joshbrew/Digital-Spectroscope/demo_app/src/assets/chickenbreast.png

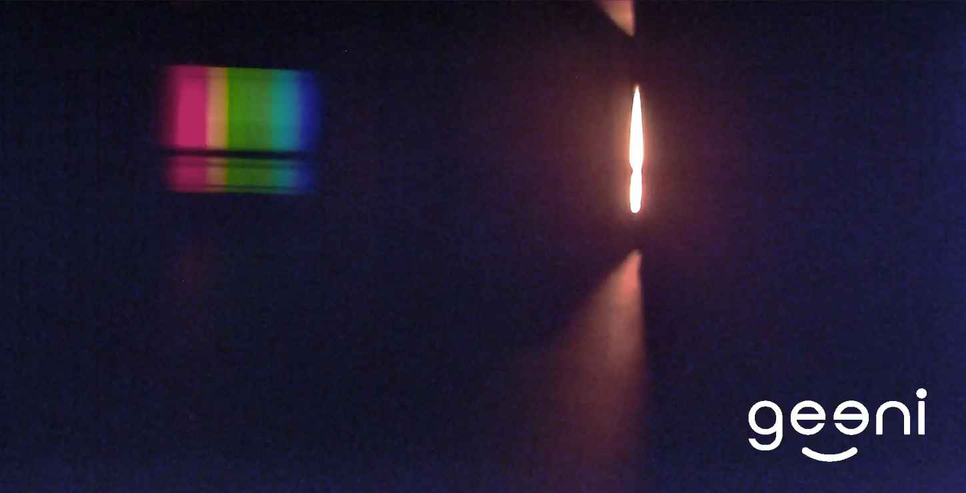
demo_app/src/assets/chickenbreast.png
