joshbrew/Digital-Spectroscope/demo_app/src/assets/chickenfat.png

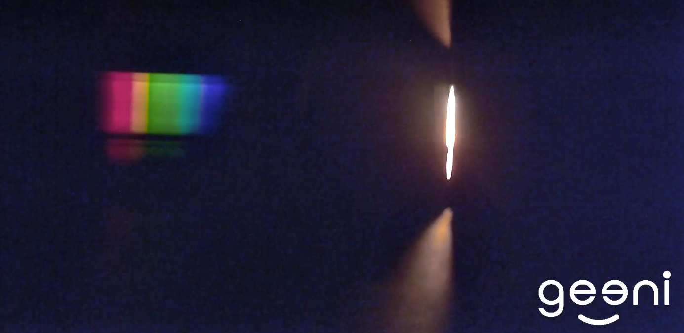
demo_app/src/assets/chickenfat.png
