joshbrew/Digital-Spectroscope/demo_app/src/assets/shrimp.jpg

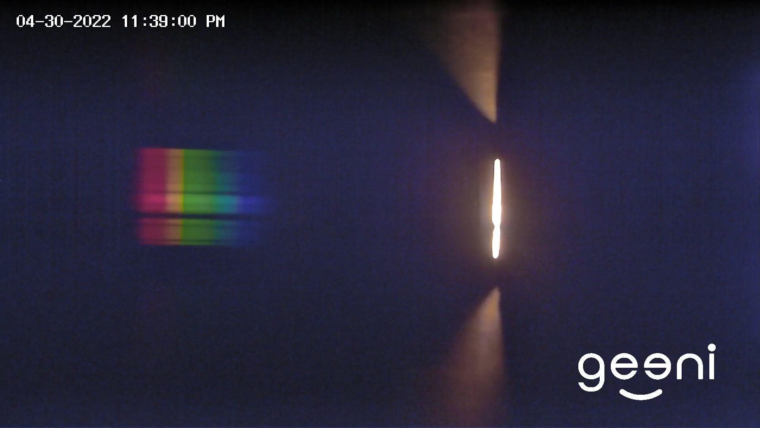
demo_app/src/assets/shrimp.jpg
