joshbrew/Digital-Spectroscope/demo_app/src/assets/spectrograms/chickenbreastspect.PNG

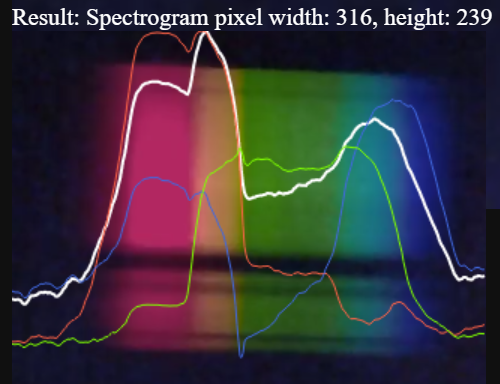
demo_app/src/assets/spectrograms/chickenbreastspect.PNG
