joshbrew/Digital-Spectroscope/screenshots/cura.PNG

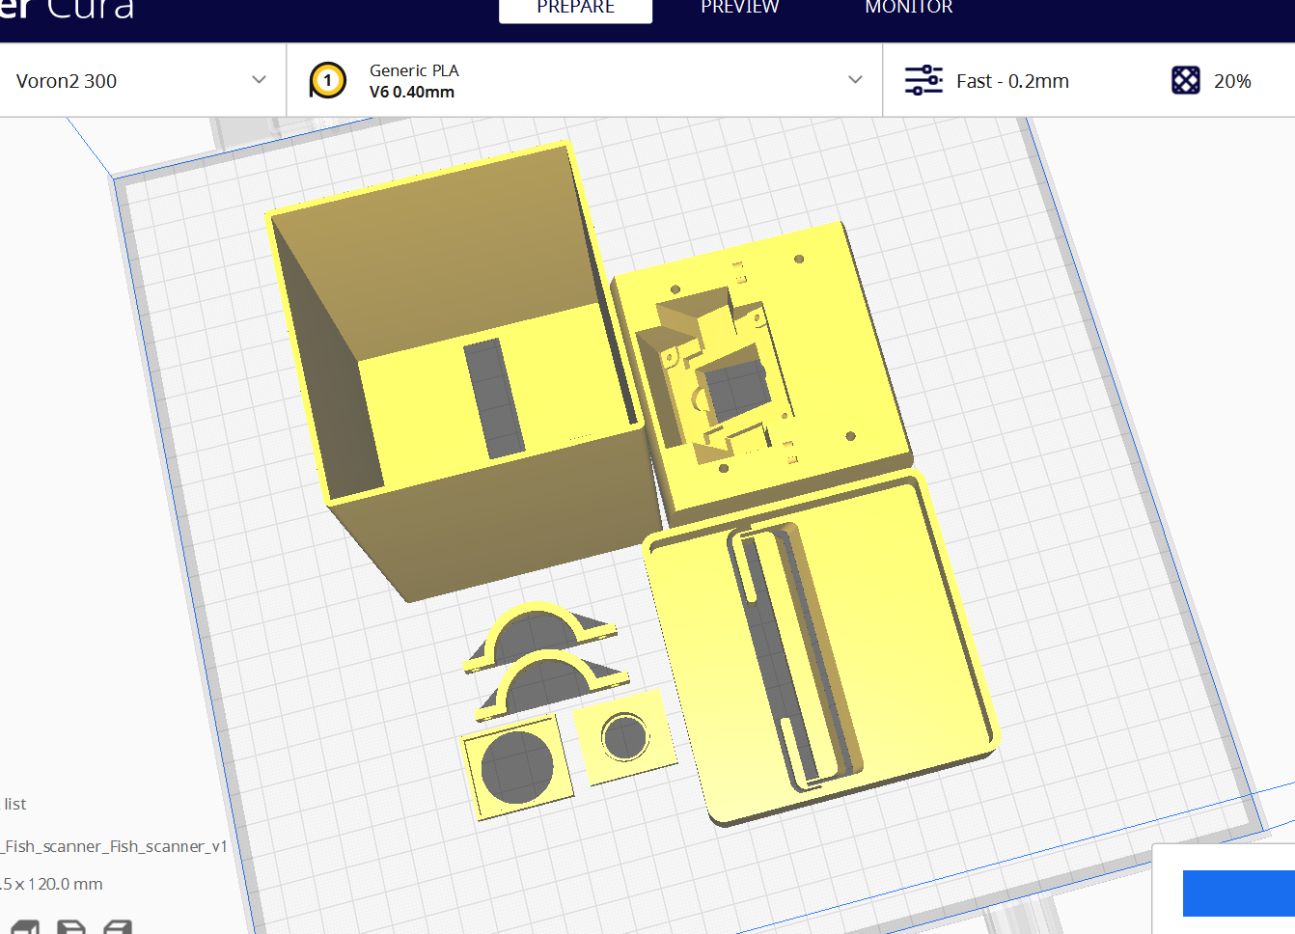
screenshots/cura.PNG
