joshbrew/Digital-Spectroscope/screenshots/hyperspectral/agate.webp

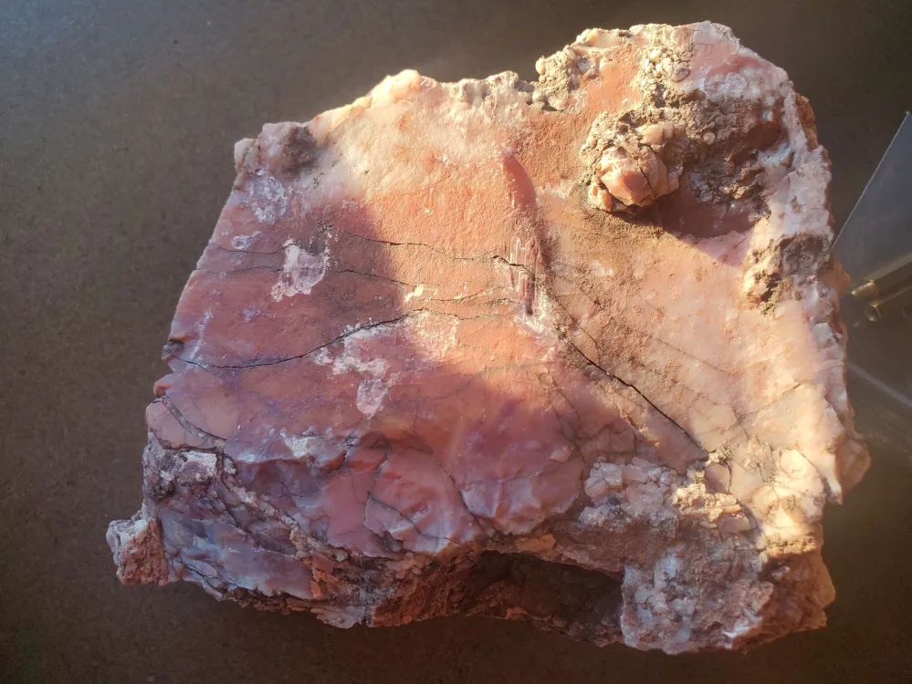
screenshots/hyperspectral/agate.webp
