joshbrew/Digital-Spectroscope/screenshots/hyperspectral/scan0_3.webp

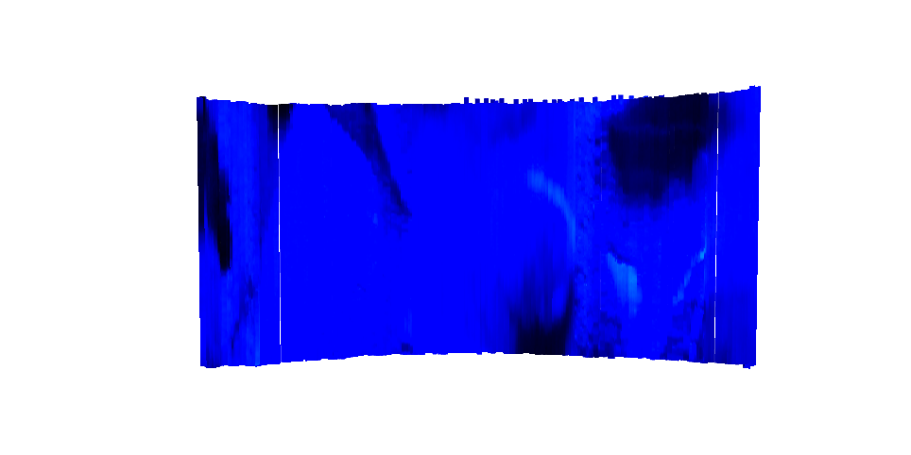
screenshots/hyperspectral/scan0_3.webp
