joshbrew/Digital-Spectroscope/screenshots/hyperspectral/scan0_4.webp

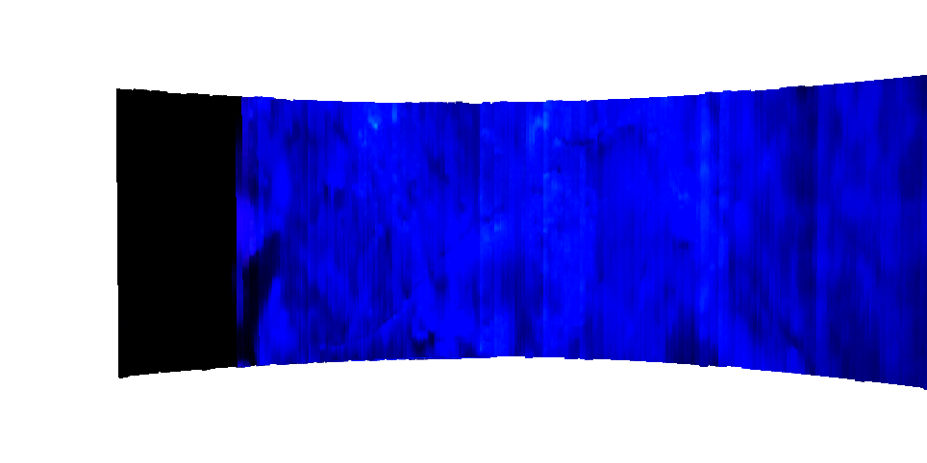
screenshots/hyperspectral/scan0_4.webp
