joshbrew/Digital-Spectroscope/screenshots/hyperspectral/scan0_5.webp

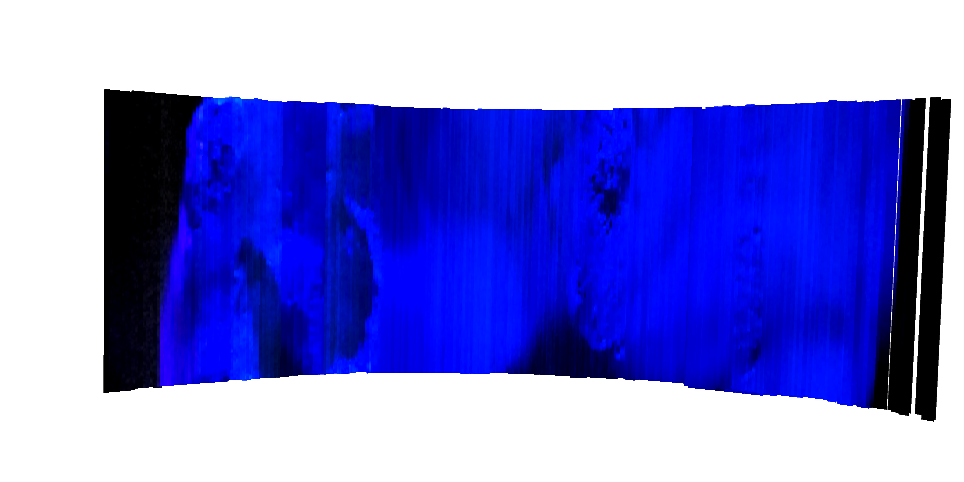
screenshots/hyperspectral/scan0_5.webp
