joshbrew/Digital-Spectroscope/screenshots/hyperspectral/scan0_8.webp

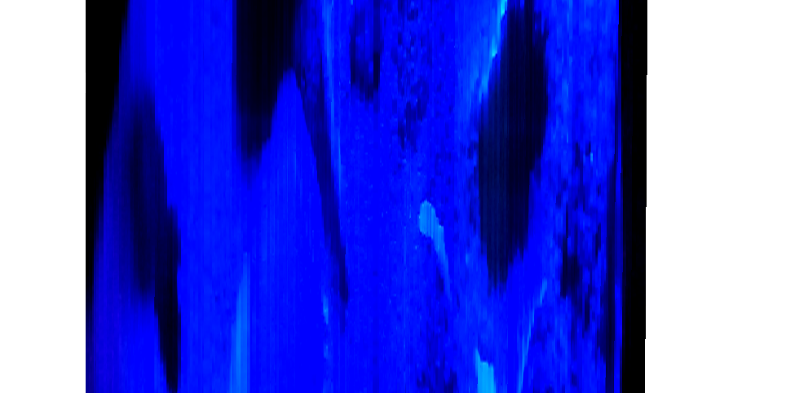
screenshots/hyperspectral/scan0_8.webp
