joshbrew/Digital-Spectroscope/screenshots/hyperspectral/scan1_5.webp

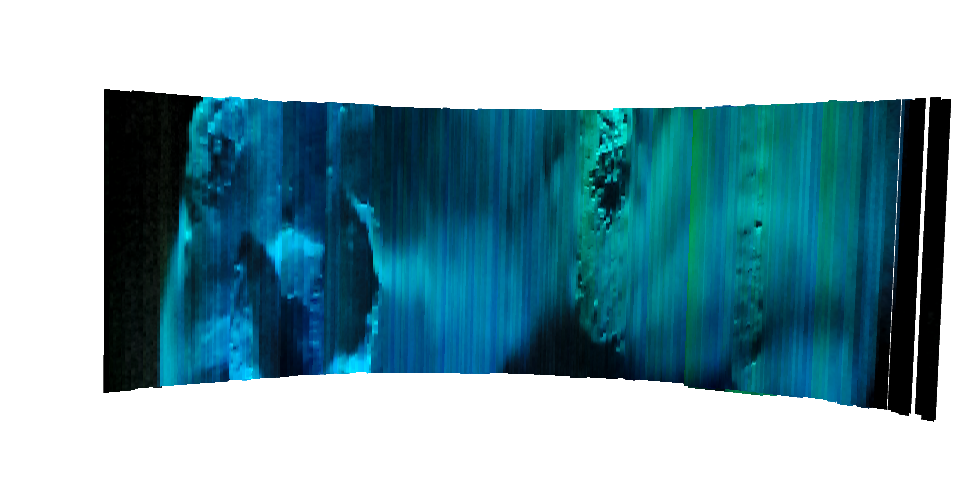
screenshots/hyperspectral/scan1_5.webp
