joshbrew/Digital-Spectroscope/screenshots/hyperspectral/scan1_8.webp

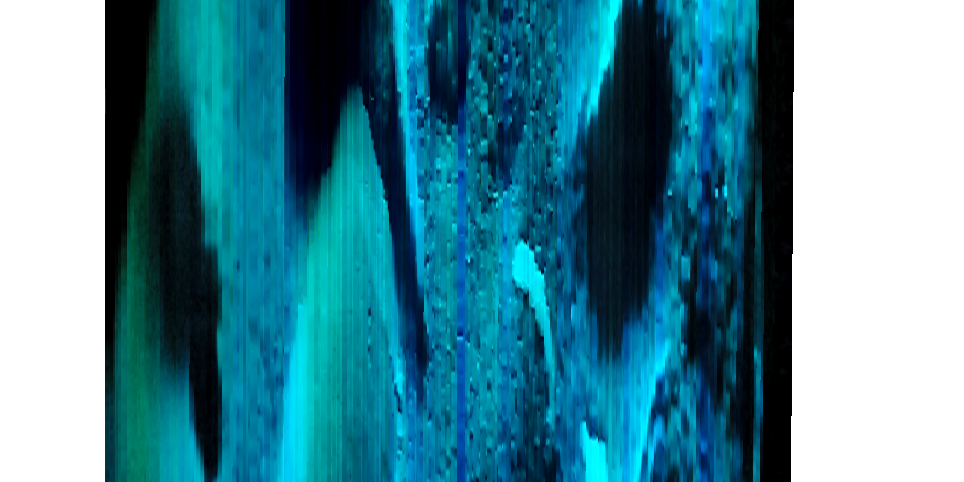
screenshots/hyperspectral/scan1_8.webp
