joshbrew/Digital-Spectroscope/screenshots/hyperspectral/scan2_4.webp

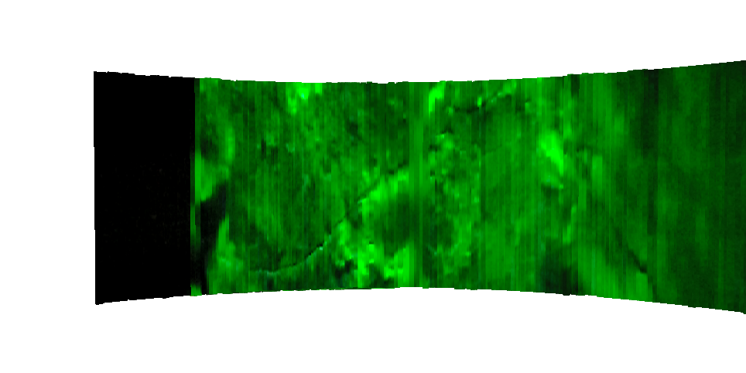
screenshots/hyperspectral/scan2_4.webp
