joshbrew/Digital-Spectroscope/screenshots/hyperspectral/scan3_4.webp

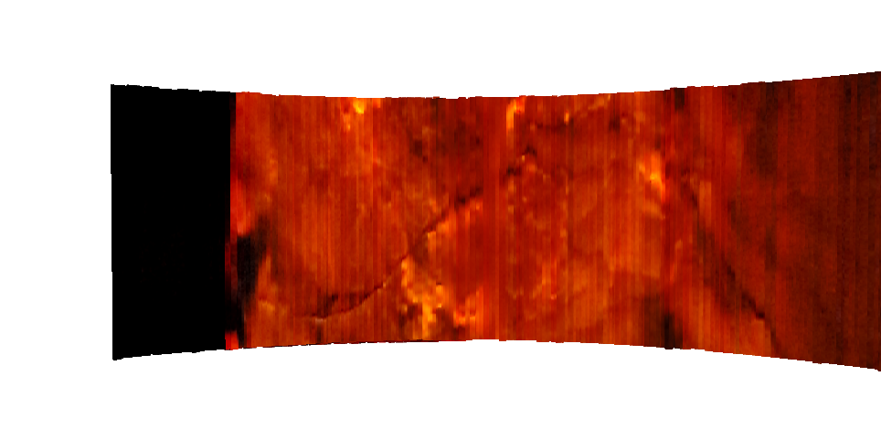
screenshots/hyperspectral/scan3_4.webp
