joshbrew/Digital-Spectroscope/screenshots/hyperspectral/scan3_5.webp

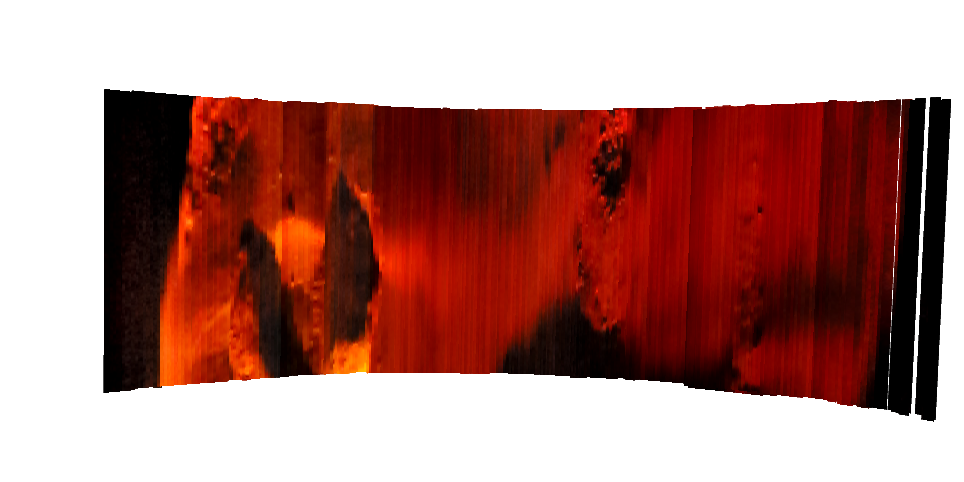
screenshots/hyperspectral/scan3_5.webp
