joshbrew/Digital-Spectroscope/screenshots/hyperspectral/scan3_8.webp

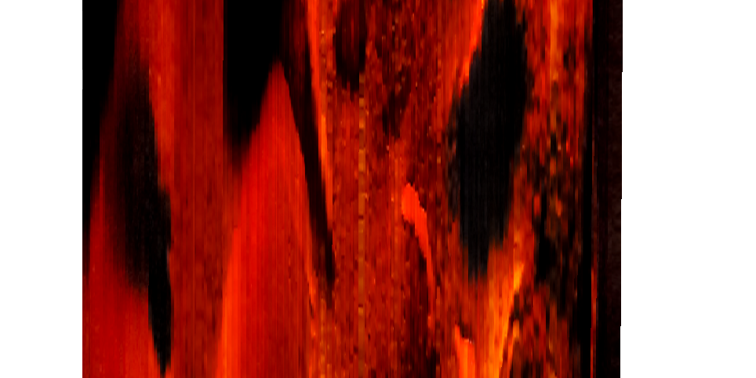
screenshots/hyperspectral/scan3_8.webp
