joshbrew/Digital-Spectroscope/screenshots/image-1.png

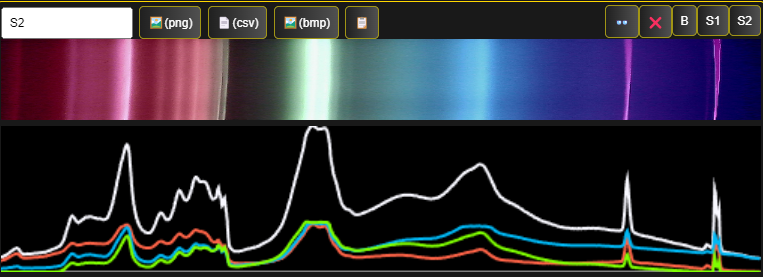
screenshots/image-1.png
