joshbrew/Digital-Spectroscope/3D_PRINTABLE/Main Modules/Smartphone Spectrometer 3D Printed Parts/Phone_Clamp_Top.stl

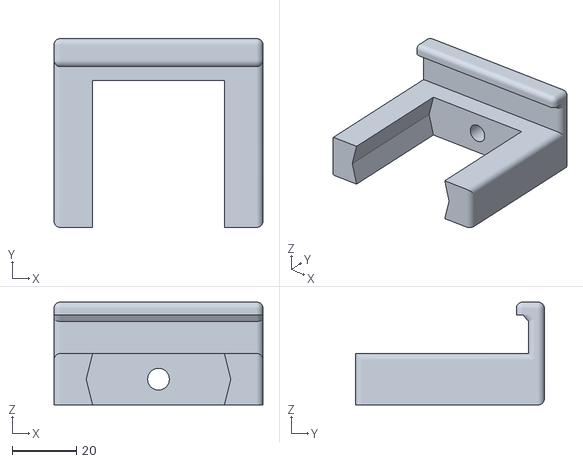
[picture p56: CAD file, 2024-03-18]
3D_PRINTABLE/Main Modules/Smartphone Spectrometer 3D Printed Parts/Phone_Clamp_Top.stl
65.0 x 58.7 x 32.0
