joshbrew/Digital-Spectroscope/3D_PRINTABLE/PhoneMiniSpectrometer/pocketTubeMount.3mf

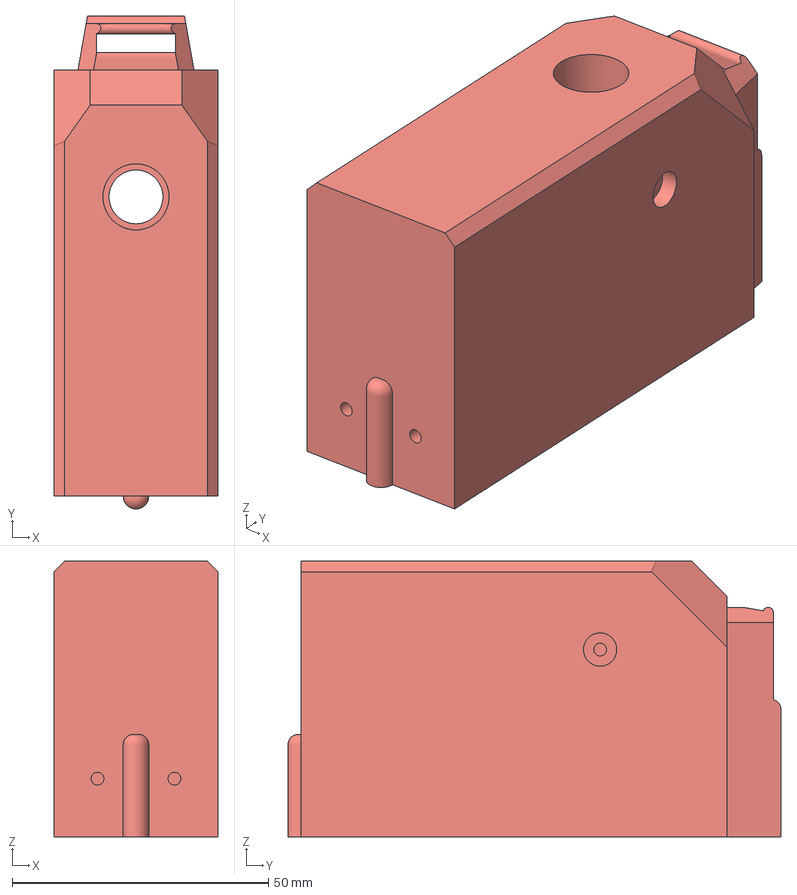
[picture p57: CAD file, 2026-05-04]
3D_PRINTABLE/PhoneMiniSpectrometer/pocketTubeMount.3mf
32.0 x 96.2 x 53.8 mm
