joshbrew/Digital-Spectroscope/3D_PRINTABLE/PocketVersion/PySpectrometer2 Benchtop Spectrometer Frame Rev 1.step

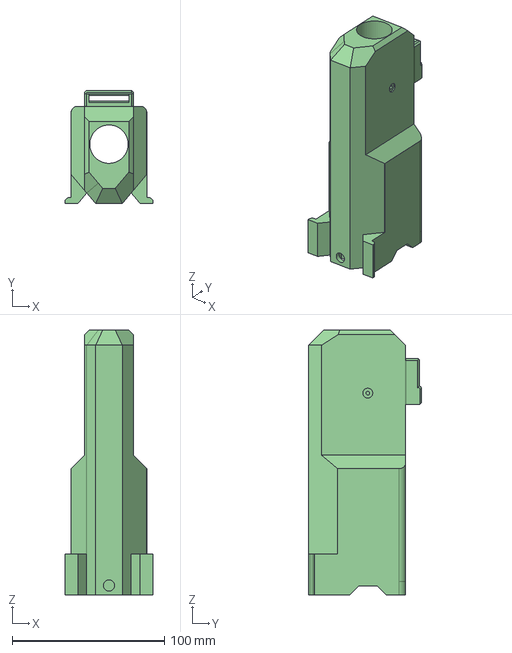
[picture p58: CAD file, 2026-05-04]
3D_PRINTABLE/PocketVersion/PySpectrometer2 Benchtop Spectrometer Frame Rev 1.step
58.0 x 74.3 x 174.0 mm
