joshbrew/Digital-Spectroscope/3D_PRINTABLE/M12_Mounts/18mm M12 Lens Holder.stl

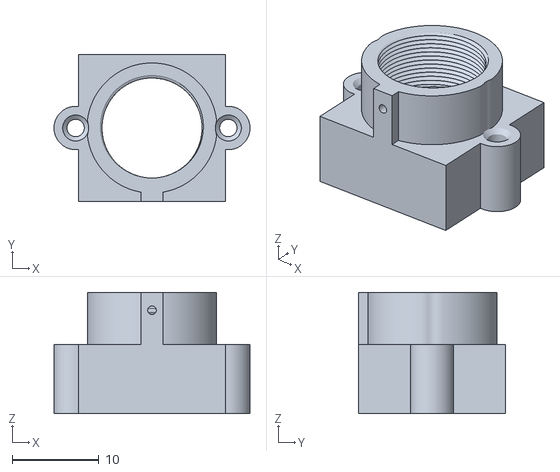
[picture p59: CAD file, 2024-03-18]
3D_PRINTABLE/M12_Mounts/18mm M12 Lens Holder.stl
22.6 x 17.0 x 14.0
