joshbrew/Digital-Spectroscope/3D_PRINTABLE/M12_Mounts/Adapter_Rings/M12m5_-_Part_1.stl

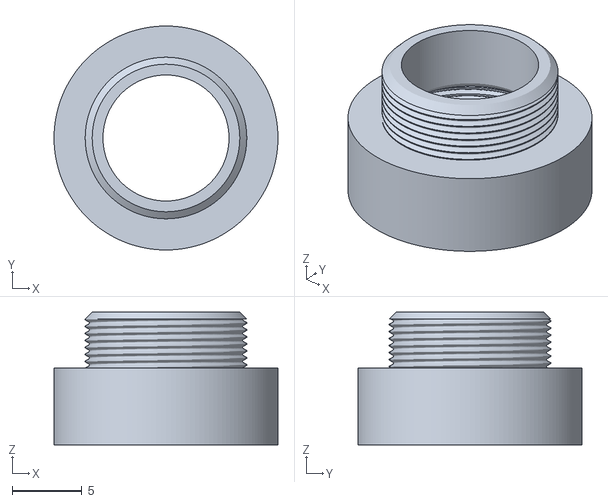
[picture p60: CAD file, 2024-03-18]
3D_PRINTABLE/M12_Mounts/Adapter_Rings/M12m5_-_Part_1.stl
16.0 x 16.0 x 9.50
