joshbrew/Digital-Spectroscope/3D_PRINTABLE/Main Modules/Arducam Spectrometer 3D Printed Parts/Camera_Mount.stl

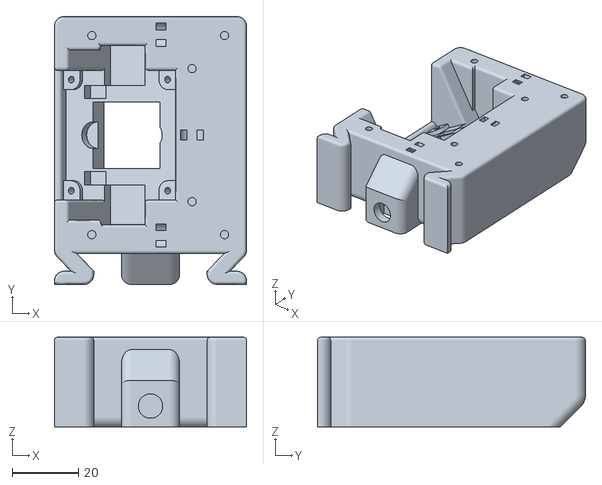
[picture p61: CAD file, 2024-03-18]
3D_PRINTABLE/Main Modules/Arducam Spectrometer 3D Printed Parts/Camera_Mount.stl
58.0 x 80.8 x 27.0
