joshbrew/Digital-Spectroscope/3D_PRINTABLE/Main Modules/Phone_Spectrometer_Mount_Cura.3mf

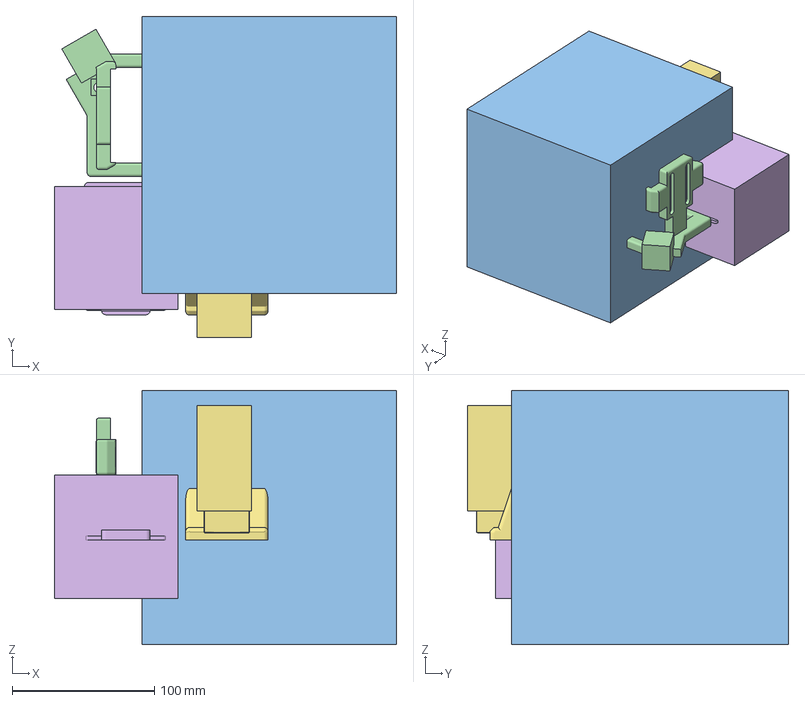
[picture p62: CAD file, 2024-03-18]
3D_PRINTABLE/Main Modules/Phone_Spectrometer_Mount_Cura.3mf
240.3 x 225.2 x 178.8 mm
Phone_Spectrometer_Mount_Cura.3mf
Phone_Spectrometer_Mount_Cura.3mf(1)
Phone_Spectrometer_Mount_Cura.3mf(4)
Phone_Spectrometer_Mount_Cura.3mf(5)
Phone_Spectrometer_Mount_Cura.3mf(6)
Phone_Spectrometer_Mount_Cura.3mf(7)
Central_Frame_SP.stl
Diffraction_Cap.stl
Phone_Clamp_Bottom.stl
