joshbrew/Digital-Spectroscope/3D_PRINTABLE/Main Modules/Smartphone Spectrometer 3D Printed Parts/Aperture_Cover.stl

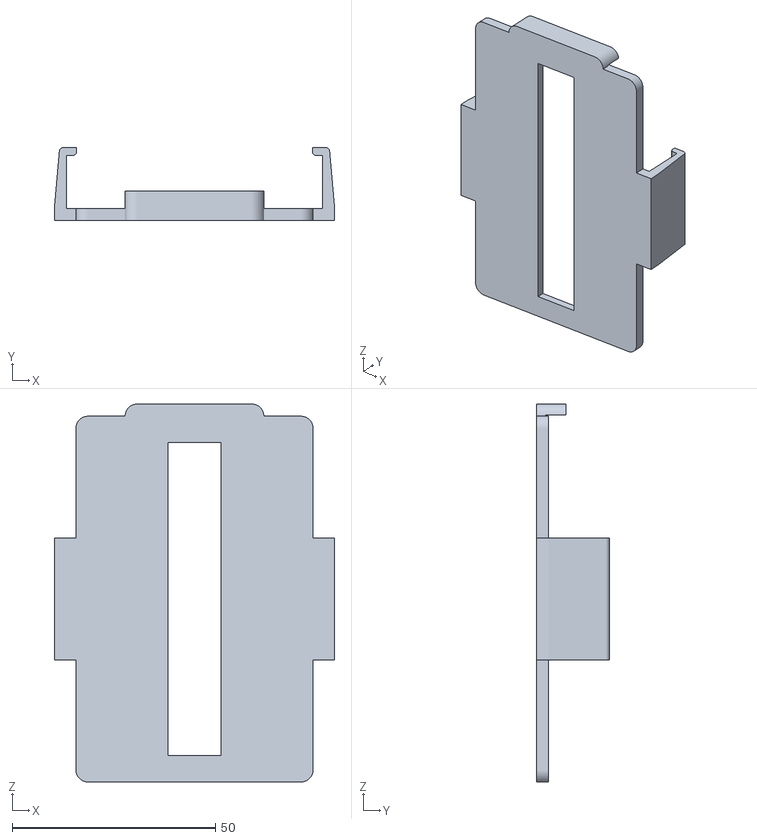
[picture p63: CAD file, 2024-03-18]
3D_PRINTABLE/Main Modules/Smartphone Spectrometer 3D Printed Parts/Aperture_Cover.stl
69.0 x 18.0 x 93.0
