joshbrew/Digital-Spectroscope/3D_PRINTABLE/PhoneMiniSpectrometer/benchtopTubeMount.3mf

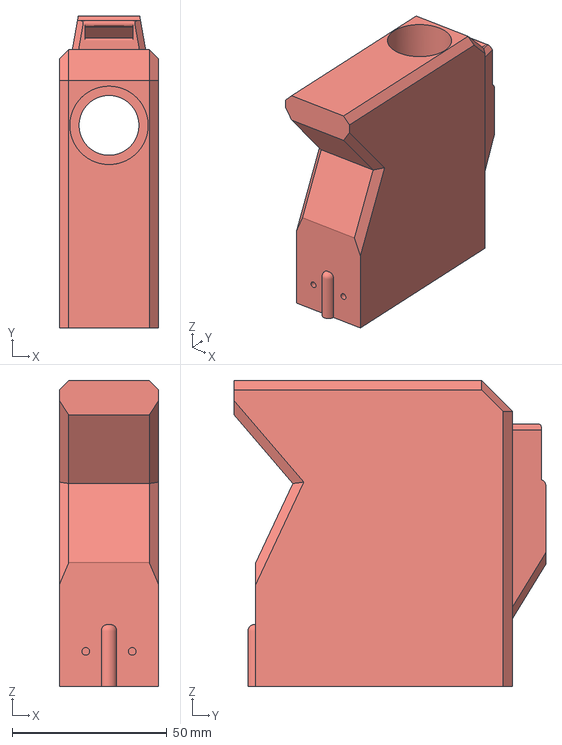
[picture p64: CAD file, 2026-05-04]
3D_PRINTABLE/PhoneMiniSpectrometer/benchtopTubeMount.3mf
32.0 x 100.7 x 98.8 mm
