joshbrew/Digital-Spectroscope/3D_PRINTABLE/PocketVersion/PySpectrometer2 Pocket Spectrometer Frame Rev 1.step

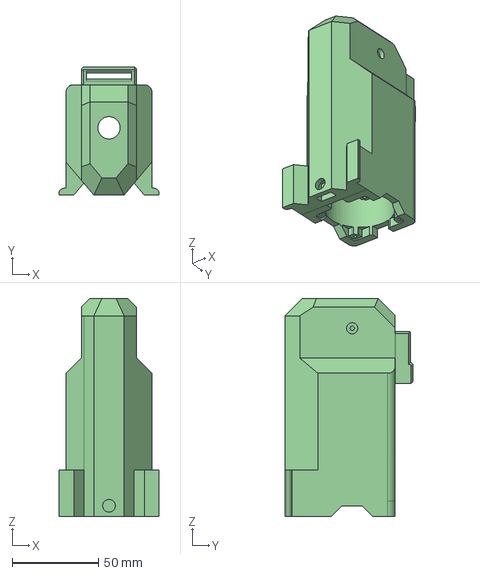
[picture p65: CAD file, 2026-05-04]
3D_PRINTABLE/PocketVersion/PySpectrometer2 Pocket Spectrometer Frame Rev 1.step
58.0 x 74.3 x 126.3 mm
