joshbrew/Digital-Spectroscope/3D_PRINTABLE/M12_Mounts/18mm M12 Lens Mount - Beveled.stl

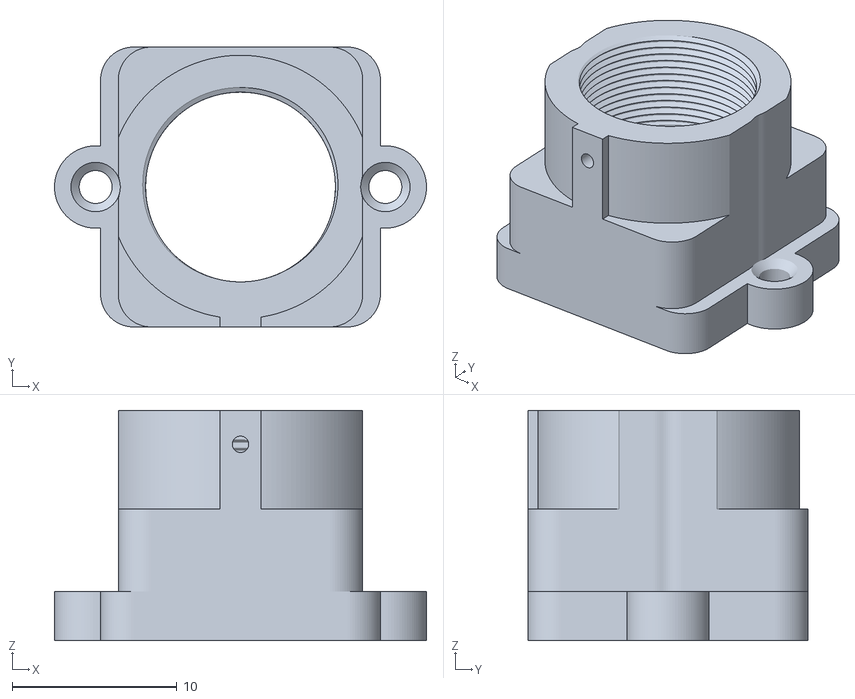
[picture p66: CAD file, 2024-03-18]
3D_PRINTABLE/M12_Mounts/18mm M12 Lens Mount - Beveled.stl
22.6 x 17.0 x 14.0
