joshbrew/Digital-Spectroscope/3D_PRINTABLE/M12_Mounts/Adapter_Rings/m12casquillo2_1.stl

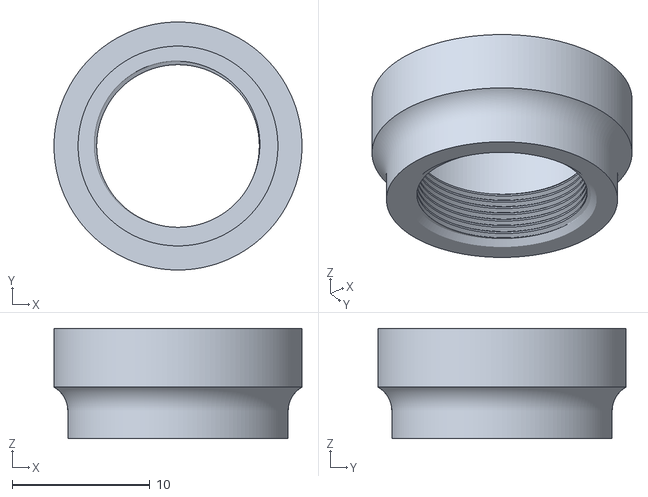
[picture p67: CAD file, 2024-03-18]
3D_PRINTABLE/M12_Mounts/Adapter_Rings/m12casquillo2_1.stl
18.0 x 18.0 x 8.00
