joshbrew/Digital-Spectroscope/3D_PRINTABLE/Main Modules/Arducam Spectrometer 3D Printed Parts/Grating_Holder_Outer.stl

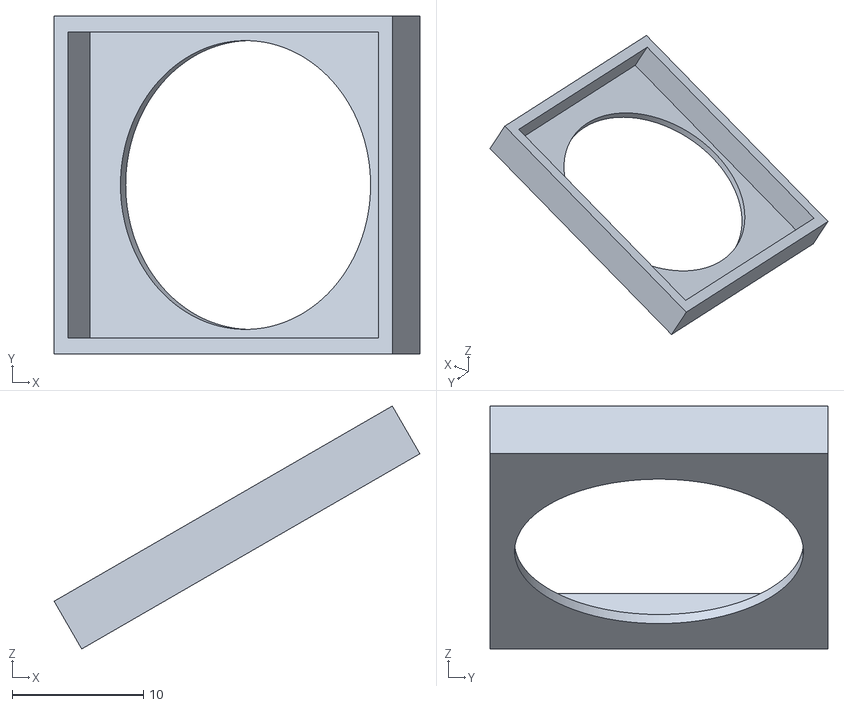
[picture p68: CAD file, 2024-03-18]
3D_PRINTABLE/Main Modules/Arducam Spectrometer 3D Printed Parts/Grating_Holder_Outer.stl
27.9 x 25.8 x 18.5
