joshbrew/Digital-Spectroscope/3D_PRINTABLE/Main Modules/Lens_Cap_Grating.3mf

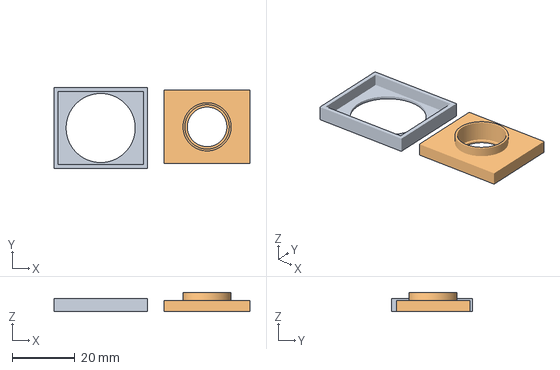
[picture p69: CAD file, 2024-03-18]
3D_PRINTABLE/Main Modules/Lens_Cap_Grating.3mf
62.5 x 25.8 x 6.20 mm
V300_Fish_scanner_Fish_scanner_v1.3mf(5)
V300_Fish_scanner_Fish_scanner_v1.3mf(6)
