joshbrew/Digital-Spectroscope/3D_PRINTABLE/Main Modules/Smartphone Spectrometer 3D Printed Parts/Central_Frame_SP.stl

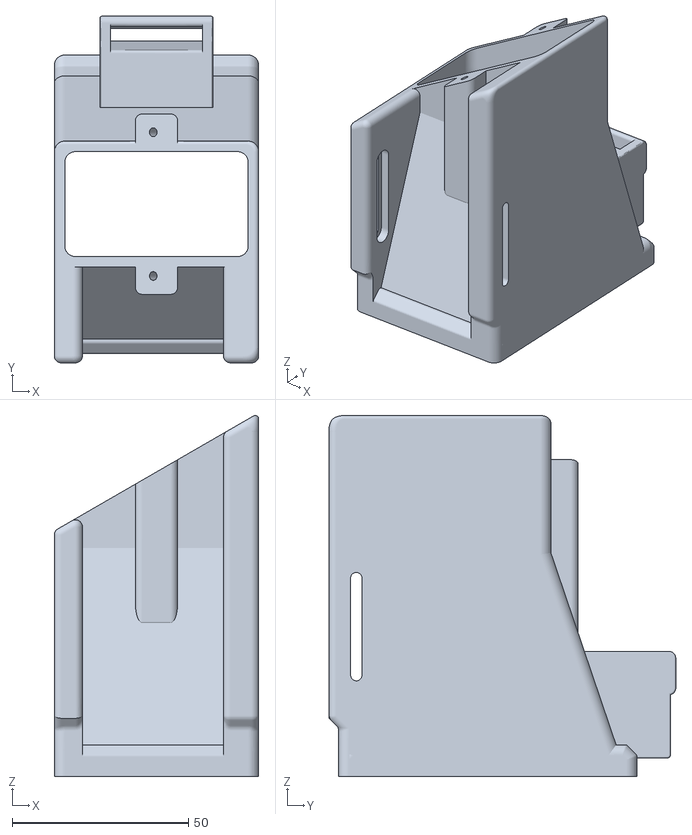
[picture p70: CAD file, 2024-03-18]
3D_PRINTABLE/Main Modules/Smartphone Spectrometer 3D Printed Parts/Central_Frame_SP.stl
58.0 x 98.3 x 102.4
