joshbrew/Digital-Spectroscope/3D_PRINTABLE/PhoneMiniSpectrometer/phoneClampBottom.3mf

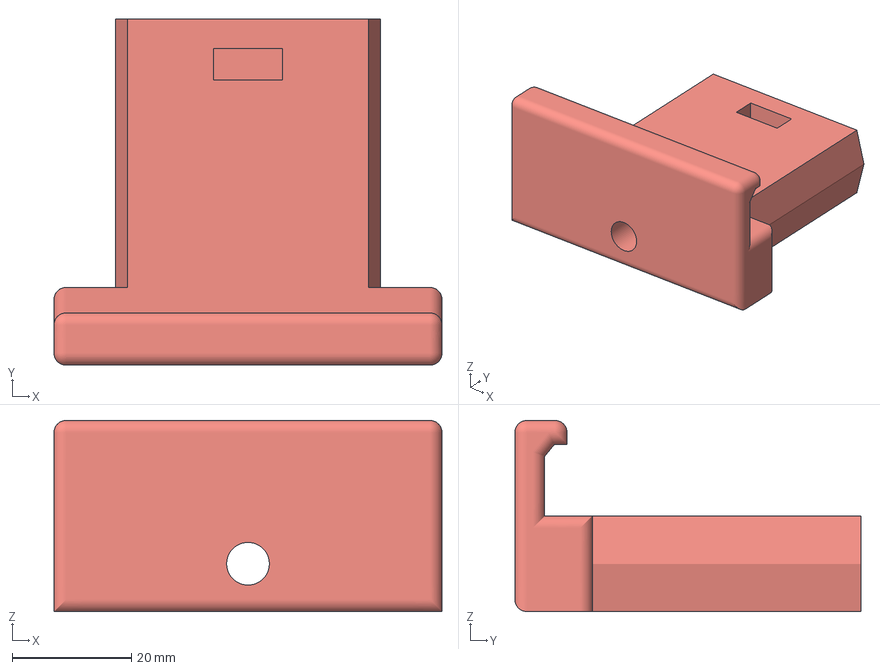
[picture p71: CAD file, 2026-05-04]
3D_PRINTABLE/PhoneMiniSpectrometer/phoneClampBottom.3mf
65.0 x 58.0 x 32.0 mm
