joshbrew/Digital-Spectroscope/3D_PRINTABLE/Main Modules/Arducam Spectrometer 3D Printed Parts/Grating_Holder_Inner.stl

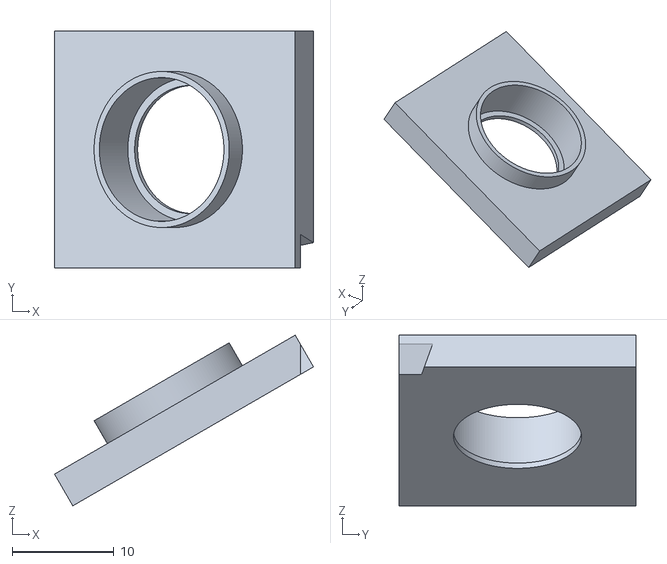
[picture p72: CAD file, 2024-03-18]
3D_PRINTABLE/Main Modules/Arducam Spectrometer 3D Printed Parts/Grating_Holder_Inner.stl
25.5 x 23.4 x 16.8
