joshbrew/Digital-Spectroscope/3D_PRINTABLE/Main Modules/Arducam_Spectrometer_Cura.3mf

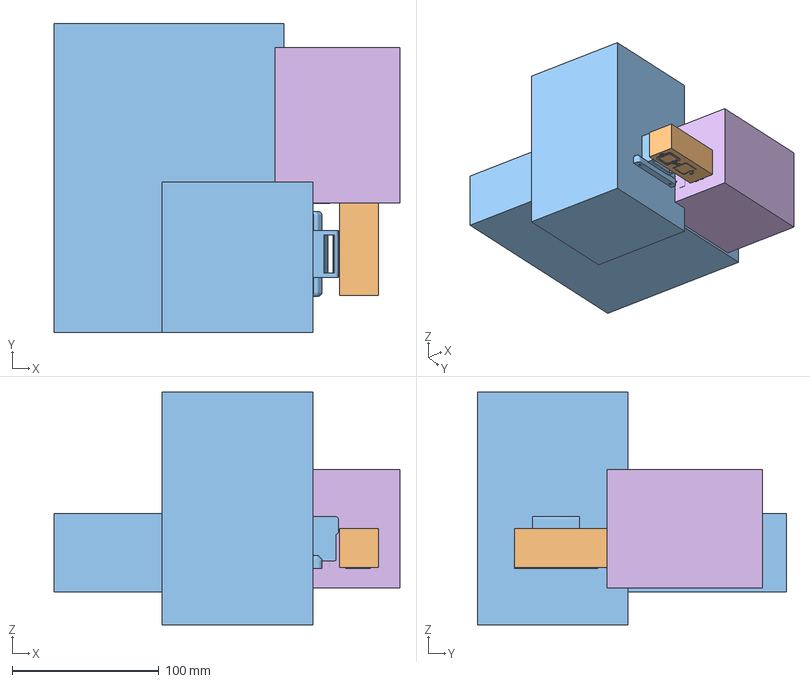
[picture p73: CAD file, 2024-03-18]
3D_PRINTABLE/Main Modules/Arducam_Spectrometer_Cura.3mf
236.2 x 211.2 x 158.7 mm
Arducam_Spectrometer_Revision2_Cura.3mf
Arducam_Spectrometer_Revision2_Cura.3mf(1)
Arducam_Spectrometer_Revision2_Cura.3mf(2)
Arducam_Spectrometer_Revision2_Cura.3mf(4)
Arducam_Spectrometer_Revision2_Cura.3mf(5)
Arducam_Spectrometer_Revision2_Cura.3mf(6)
Arducam_Spectrometer_Revision2_Cura.3mf(7)
Arducam_Spectrometer_Revision2_Cura.3mf(8)
Arducam_Spectrometer_Revision2_Cura.3mf(9)
Arducam_Spectrometer_Revision2_Cura.3mf(10)
Central_Frame_AC_Wide.stl
