joshbrew/Digital-Spectroscope/3D_PRINTABLE/PhoneMiniSpectrometer/basePlate.3mf

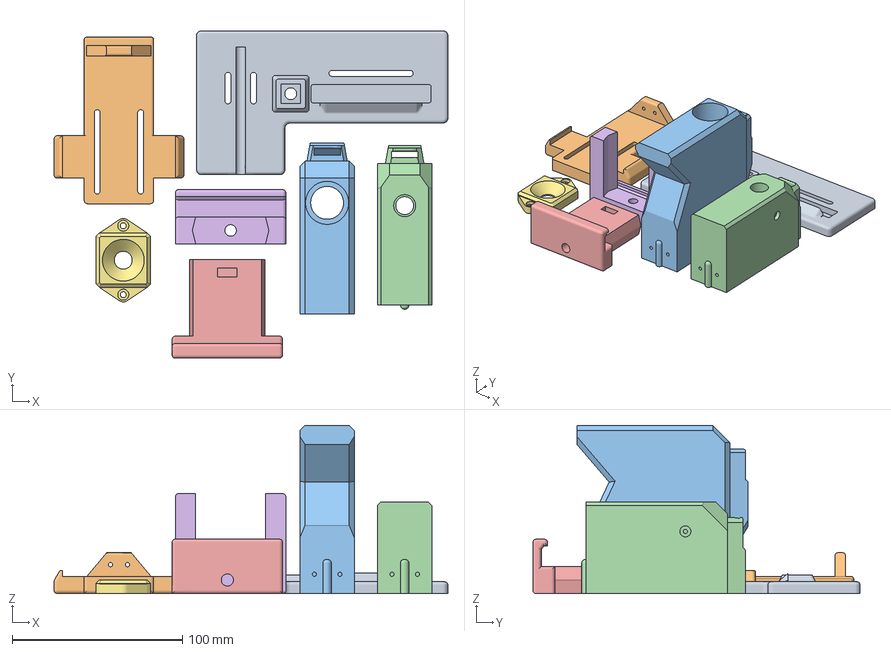
[picture p74: CAD file, 2026-05-04]
3D_PRINTABLE/PhoneMiniSpectrometer/basePlate.3mf
231.4 x 192.4 x 98.8 mm
Base Plate
Phone Clamp Rail Mount (1) (1)
Pocket Spectrometer Housing x 2
Phone Clamp Bottom
Phone Clamp Top
