joshbrew/Digital-Spectroscope/3D_PRINTABLE/Main Modules/Arducam Spectrometer 3D Printed Parts/Central_Frame_AC.stl

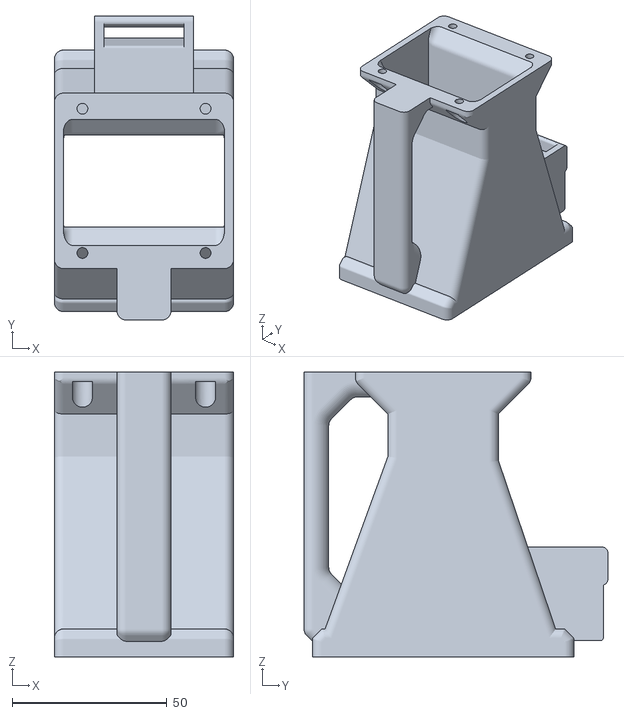
[picture p75: CAD file, 2024-03-18]
3D_PRINTABLE/Main Modules/Arducam Spectrometer 3D Printed Parts/Central_Frame_AC.stl
58.0 x 98.3 x 92.0
