joshbrew/Digital-Spectroscope/3D_PRINTABLE/Main Modules/Phone_Spectrometer_Mount_BambuStudio.3mf

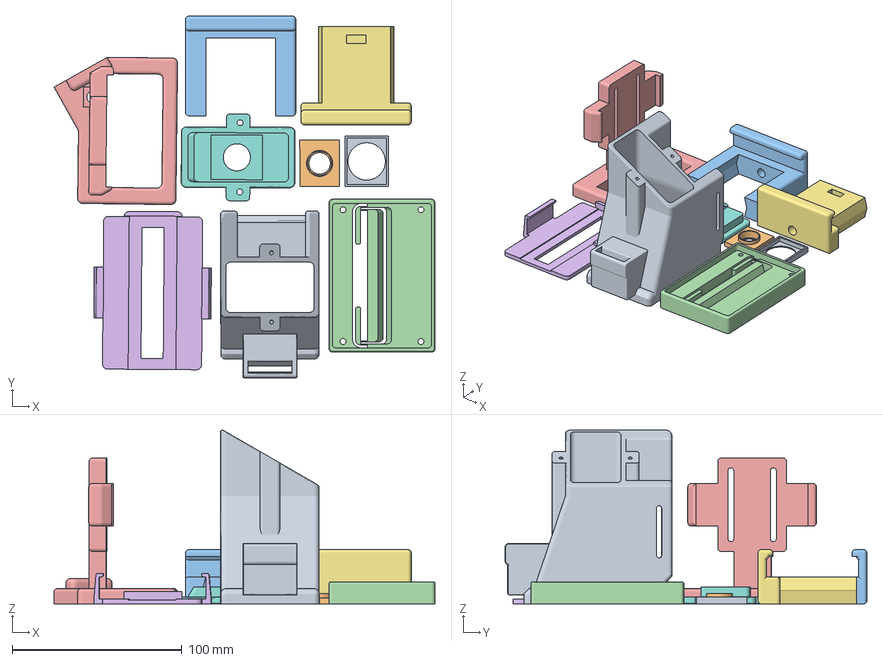
[picture p76: CAD file, 2024-03-18]
3D_PRINTABLE/Main Modules/Phone_Spectrometer_Mount_BambuStudio.3mf
224.3 x 213.0 x 102.4 mm
Phone_Spectrometer_Mount.3mf
Phone_Spectrometer_Mount.3mf(1)
Phone_Spectrometer_Mount.3mf(6)
Aperture_Cap.stl
Phone_Clamp_Base_Fixed.stl
Aperture_Cover_Clips.stl
Phone_Clamp_Bottom.stl
Diffraction_Cap.stl
Central_Frame_SP.stl
