joshbrew/Digital-Spectroscope/3D_PRINTABLE/Main Modules/Smartphone Spectrometer 3D Printed Parts/Phone_Clamp_Base.stl

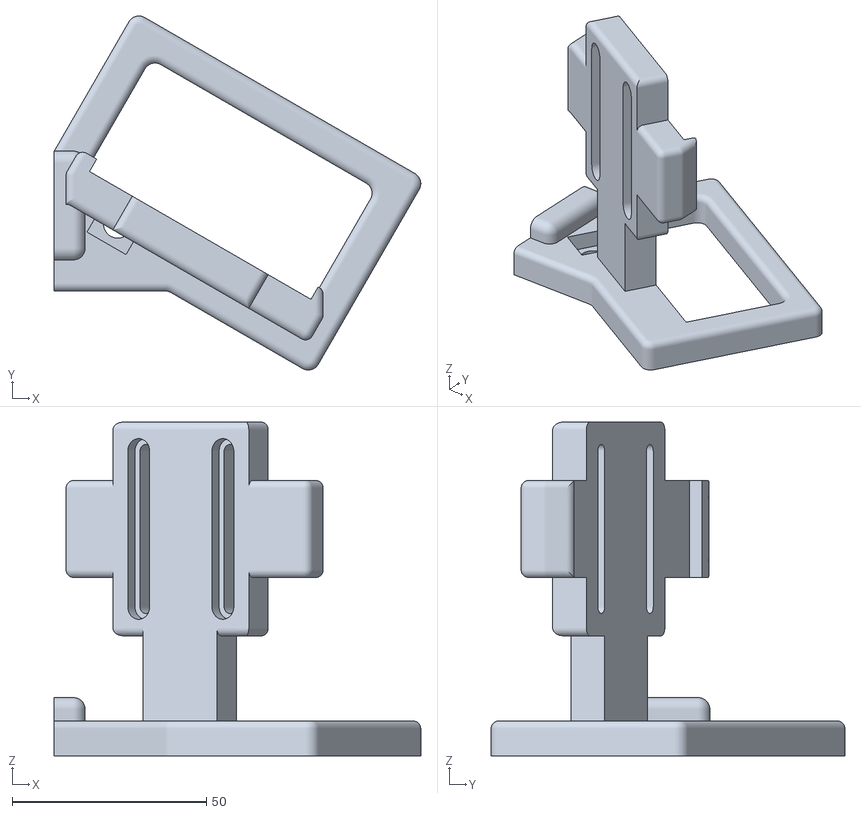
[picture p77: CAD file, 2024-03-18]
3D_PRINTABLE/Main Modules/Smartphone Spectrometer 3D Printed Parts/Phone_Clamp_Base.stl
94.3 x 91.1 x 85.9
