joshbrew/Digital-Spectroscope/3D_PRINTABLE/PhoneMiniSpectrometer/phoneClampBase.3mf

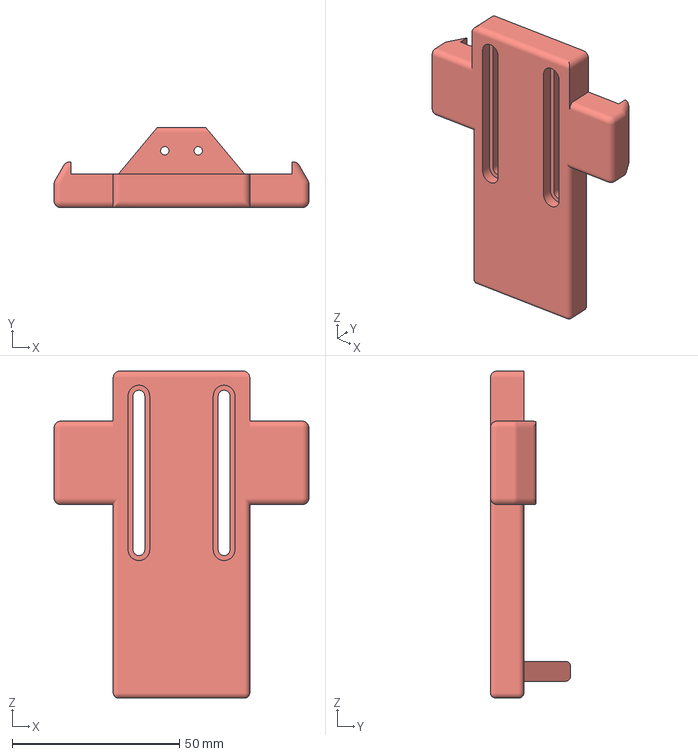
[picture p78: CAD file, 2026-05-04]
3D_PRINTABLE/PhoneMiniSpectrometer/phoneClampBase.3mf
76.3 x 24.0 x 97.9 mm
