joshbrew/Digital-Spectroscope/3D_PRINTABLE/Main Modules/Arducam Spectrometer 3D Printed Parts/Camera_Cover.stl

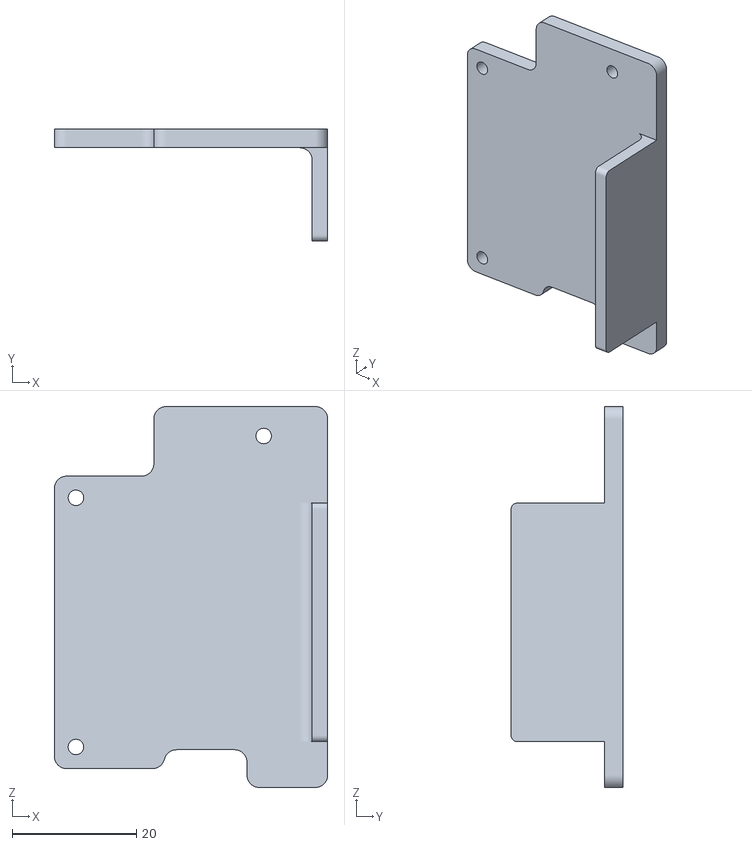
[picture p79: CAD file, 2024-03-18]
3D_PRINTABLE/Main Modules/Arducam Spectrometer 3D Printed Parts/Camera_Cover.stl
44.0 x 18.0 x 61.3
