joshbrew/Digital-Spectroscope/3D_PRINTABLE/Main Modules/petgcf_settings.PNG

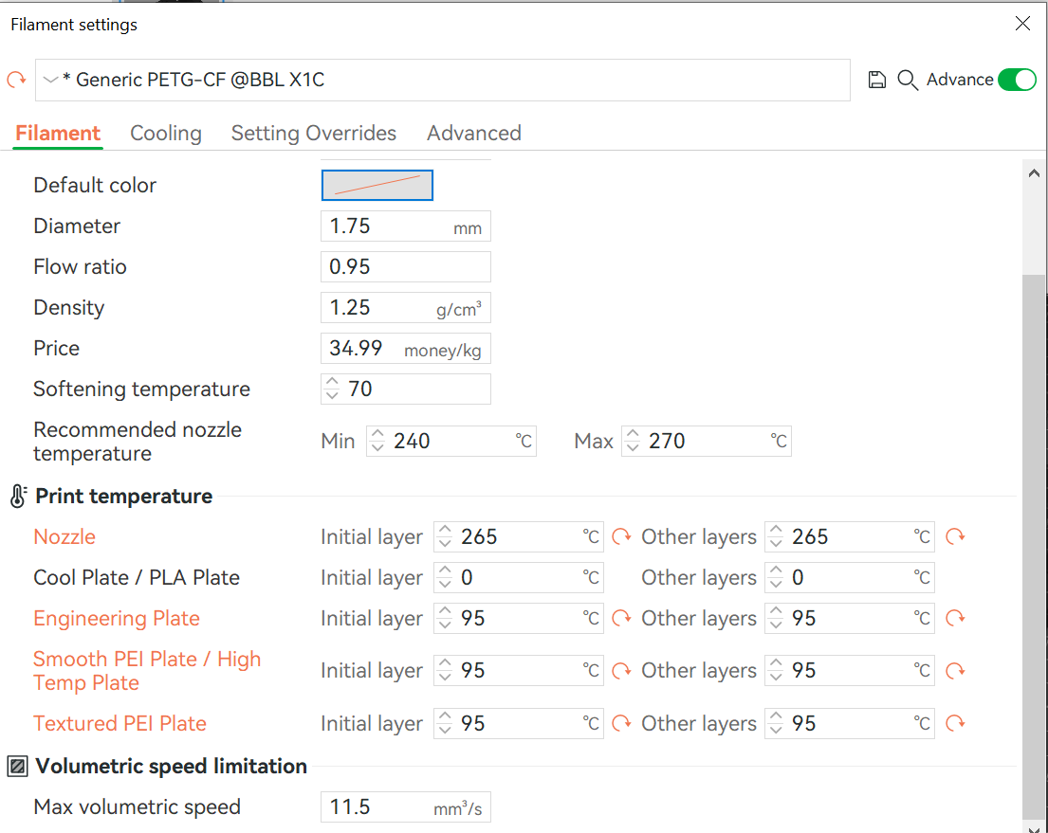
3D_PRINTABLE/Main Modules/petgcf_settings.PNG
